MBetters/cpeg498_venom/spider_arduino/examples/sonar_example/sonar_example.ino

// Pins
const int TRIG_PIN = 7;
const int ECHO_PIN = 8;
const int BUZZER_PIN = 6;


// Anything over 30 cm (1500 us pulse) is "out of range"
const unsigned int MAX_DIST = 1500;

void setup() {

  // The Trigger pin will tell the sensor to range find
  pinMode(TRIG_PIN, OUTPUT);
  digitalWrite(TRIG_PIN, LOW);
  pinMode(BUZZER_PIN, OUTPUT);

  // Use the serial monitor to view the sensor output
  Serial.begin(9600);
}

void loop() {

  unsigned long t1;
  unsigned long t2;
  unsigned long pulse_width;
  float cm;
  float inches;

  // Hold the trigger pin high for at least 10 us
  digitalWrite(TRIG_PIN, HIGH);
  delayMicroseconds(10);
  digitalWrite(TRIG_PIN, LOW);

  // Wait for pulse on echo pin
  while ( digitalRead(ECHO_PIN) == 0 );

  // Measure how long the echo pin was held high (pulse width)
  // Note: the micros() counter will overflow after ~70 min
  t1 = micros();
  while ( digitalRead(ECHO_PIN) == 1);
  t2 = micros();
  pulse_width = t2 - t1;

  // Calculate distance in centimeters and inches. The constants
  // are found in the datasheet, and calculated from the assumed speed 
  //of sound in air at sea level (~340 m/s).
  cm = pulse_width / 58.0;
  inches = pulse_width / 148.0;

  // Print out results
  if ( pulse_width > MAX_DIST ) {
    Serial.println("Out of range");
    tone(BUZZER_PIN, 262);
  } else {
    Serial.print(cm);
    Serial.print(" cm \t");
    Serial.print(inches);
    Serial.println(" in");
    noTone(BUZZER_PIN);
  }
  
  // Wait at least 60ms before next measurement
  delay(60);
}
